Wren6991/RISCBoy/doc/diagrams/ppu_coord_screen.pdf

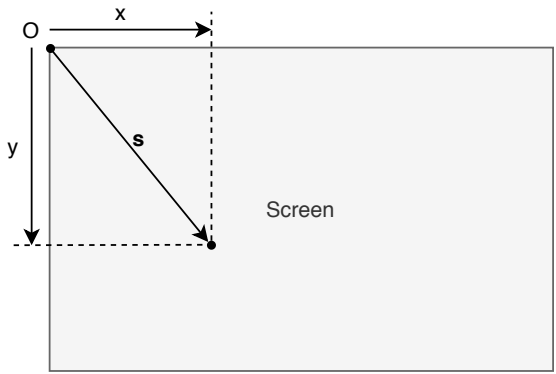
[picture p20: figure]
Screen
