Wren6991/RISCBoy/doc/diagrams/ppu_coord_texture.pdf

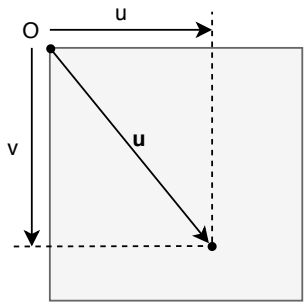
[picture p21: figure]
