Wren6991/RISCBoy/doc/diagrams/ppu_bg_coords.pdf

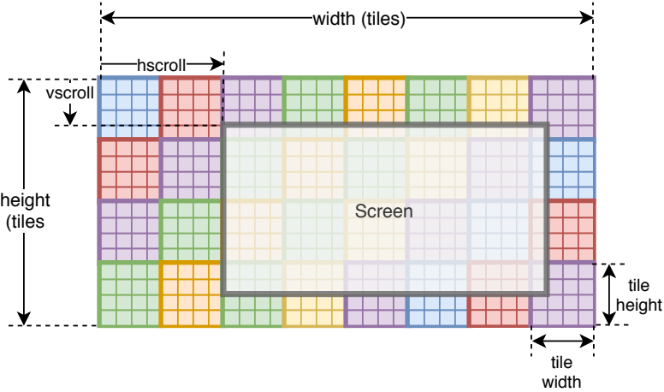
[picture p22: figure]
Screen; hscroll; vscroll; width (tiles); height (tiles; tile height; tile width
