Wren6991/RISCBoy/board/riscboy_reva0/datasheet/SPI LCD from AliExpress.jpg

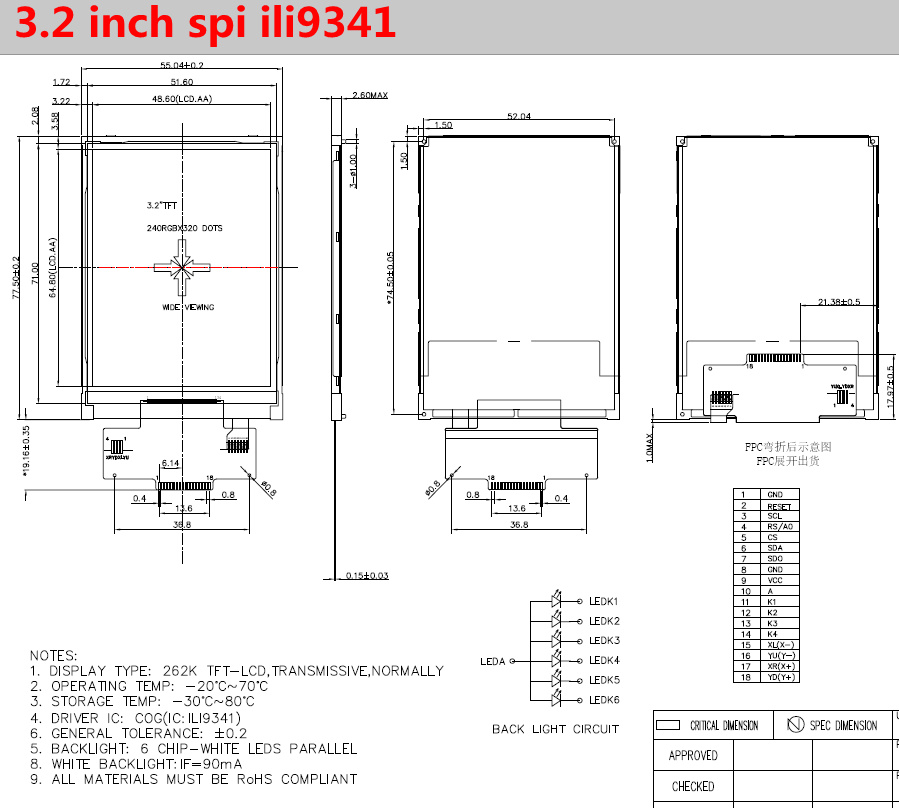
board/riscboy_reva0/datasheet/SPI LCD from AliExpress.jpg
