Wren6991/RISCBoy/software/apps/spin_demo/wilber.png

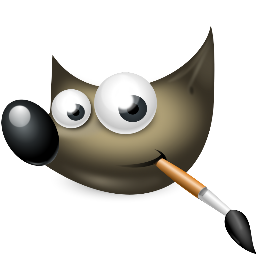
software/apps/spin_demo/wilber.png
