Wren6991/RISCBoy/software/apps/ulx3s_spin/ulx3s.png

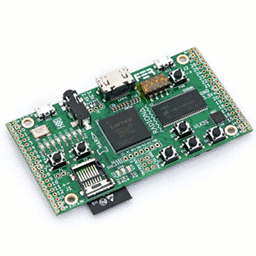
software/apps/ulx3s_spin/ulx3s.png
