Wren6991/RISCBoy/software/graphics/assets/abandonauts/tiles.png

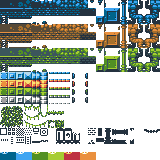
software/graphics/assets/abandonauts/tiles.png
