Wren6991/RISCBoy/software/graphics/assets/arcade_platformer/arcade_platformerV2.png

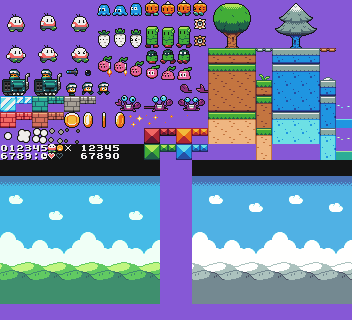
software/graphics/assets/arcade_platformer/arcade_platformerV2.png
