Wren6991/RISCBoy/software/graphics/assets/arcade_platformer/arcade_platformerV2_transparent.png

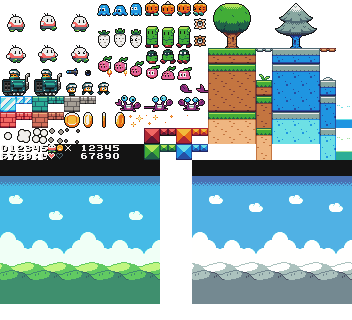
software/graphics/assets/arcade_platformer/arcade_platformerV2_transparent.png
