Wren6991/RISCBoy/software/graphics/assets/colony/colony_0.png

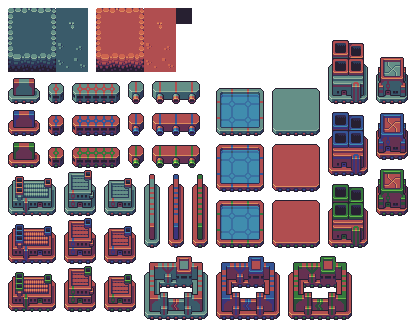
software/graphics/assets/colony/colony_0.png
