Wren6991/RISCBoy/software/graphics/assets/platformer_art_deluxe_pixel_edition/sample.png

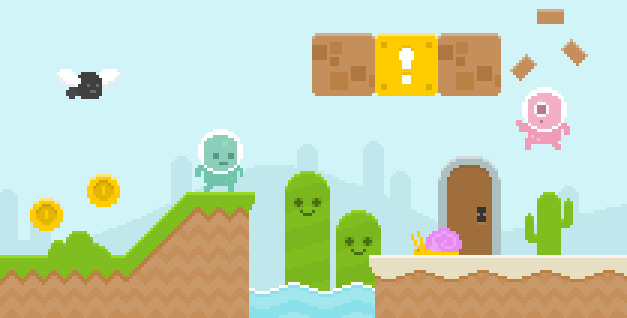
software/graphics/assets/platformer_art_deluxe_pixel_edition/sample.png
