Wren6991/RISCBoy/software/graphics/assets/platformer_art_deluxe_pixel_edition/spritesheet.png

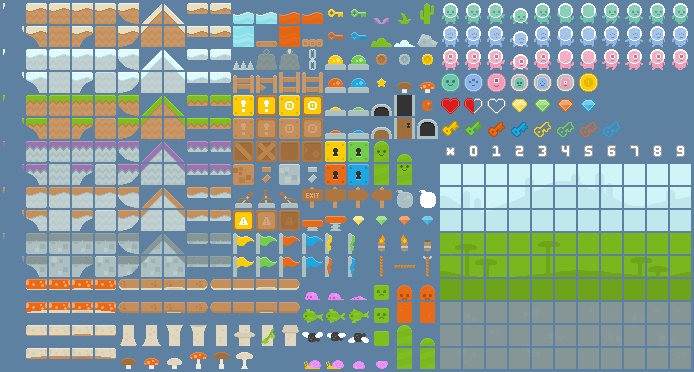
software/graphics/assets/platformer_art_deluxe_pixel_edition/spritesheet.png
