Wren6991/RISCBoy/test/ppu/testcases/blit_smoke_argb1555/expected_output.png

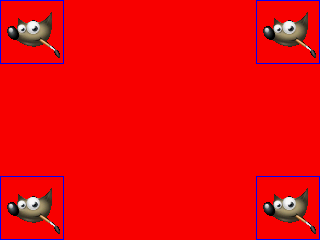
test/ppu/testcases/blit_smoke_argb1555/expected_output.png
