Wren6991/RISCBoy/test/ppu/testcases/tile_clip/expected_output.png

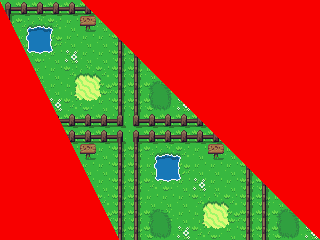
test/ppu/testcases/tile_clip/expected_output.png
