Wren6991/RISCBoy/test/ppu/testcases/tile_t16_pf128_argb1555_scrollneg/expected_output.png

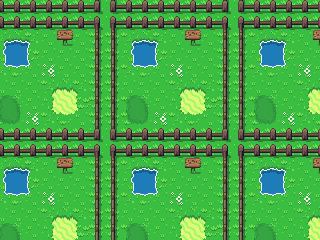
test/ppu/testcases/tile_t16_pf128_argb1555_scrollneg/expected_output.png
