Wren6991/RISCBoy/doc/diagrams/system_arch.pdf

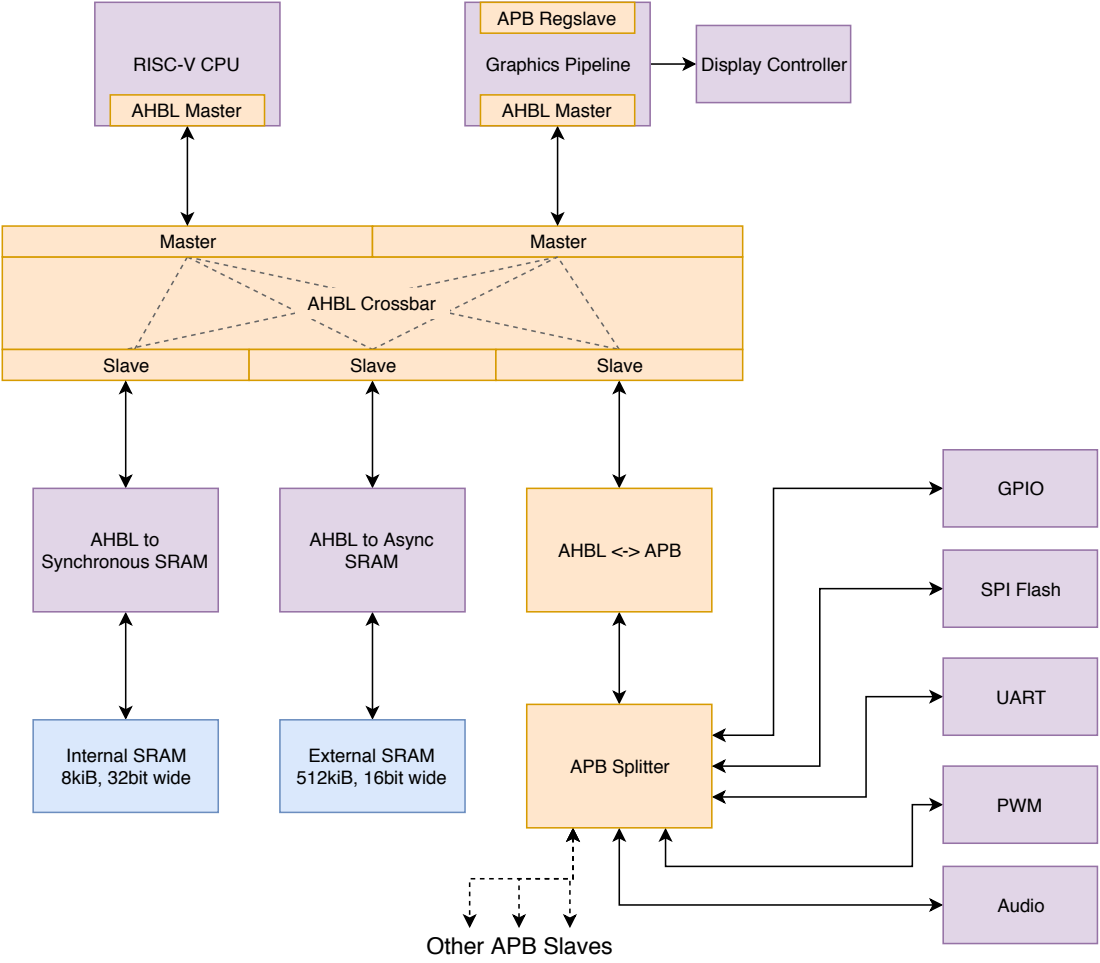
[picture p46: page 1]
Master; Slave; RISC-V CPU; AHBL Master; Graphics Pipeline; APB Regslave; Display Controller; AHBL to Synchronous SRAM; Internal SRAM 8kiB, 32bit wide; External SRAM 512kiB, 16bit wide; AHBL <-> APB; APB Splitter; UART; PWM; Audio; GPIO; AHBL Crossbar; SPI Flash

AHBL to Async
SRAM

Other APB Slaves
