Wren6991/RISCBoy/doc/diagrams/cpu_backend.pdf

Stage D | Clock
Stage M | Clock

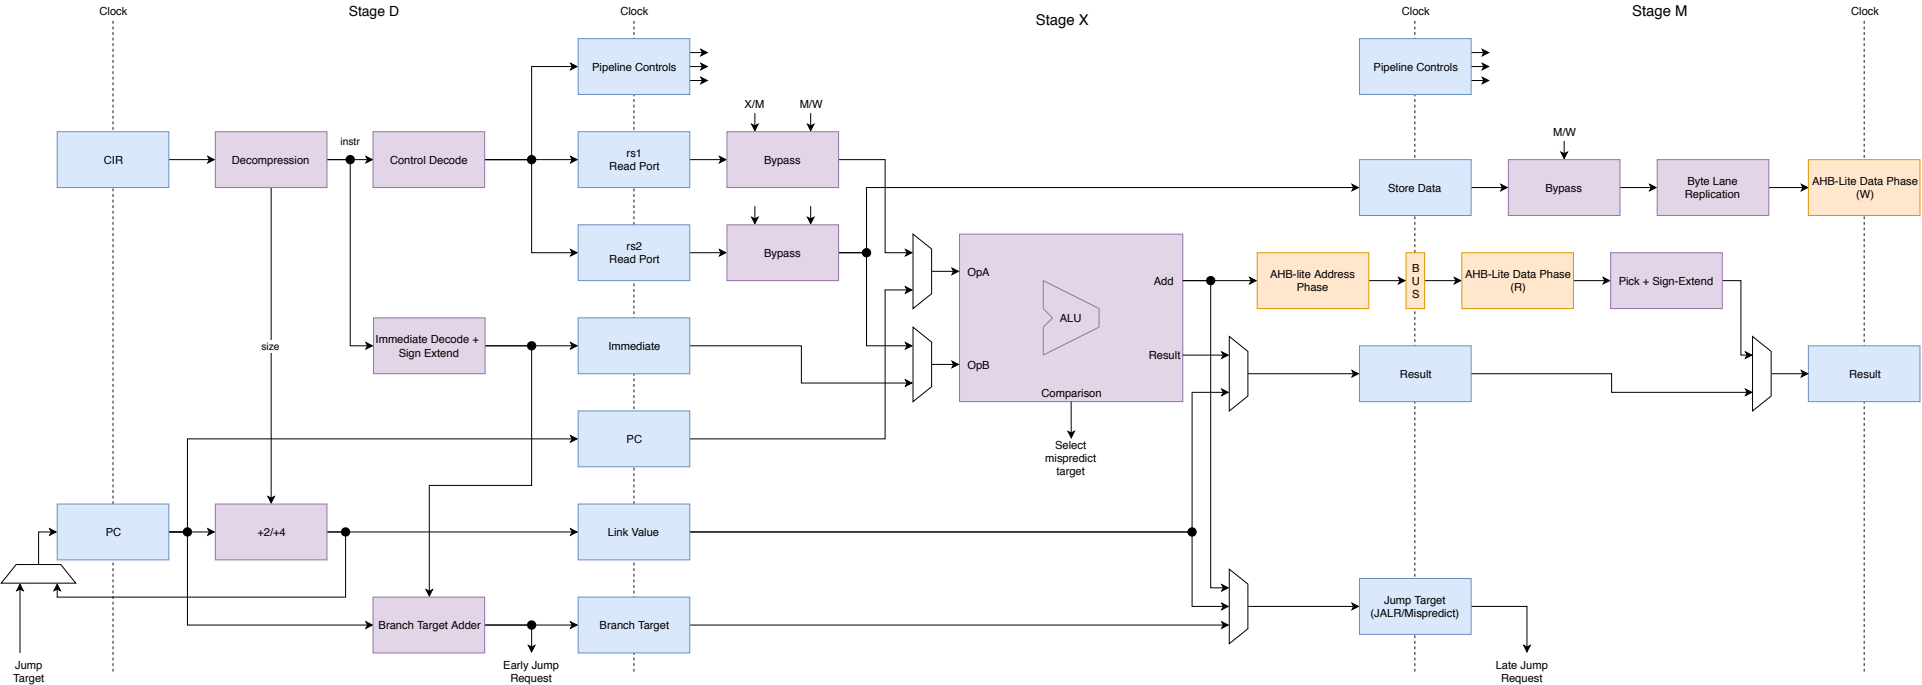
[picture p47: page 1]
rs1 Read Port; rs2 Read Port; CIR; size; instr; Decompression; Branch Target; Link Value; Immediate; Control Decode; Immediate Decode + Sign Extend; Pipeline Controls; Clock; Stage X Clock; ALU; OpA; OpB; Add; Comparison; Result; Bypass; Early Jump Request; Jump Target; Jump Target (JALR/Mispredict); Late Jump Request; Store Data; Byte Lane Replication; Select mispredict target

AHB-Lite Data Phase

AHB-lite Address
Phase

Pick + Sign-Extend

Branch Target Adder
