Wren6991/RISCBoy/board/sram_dev_board/sram_dev_board.pdf

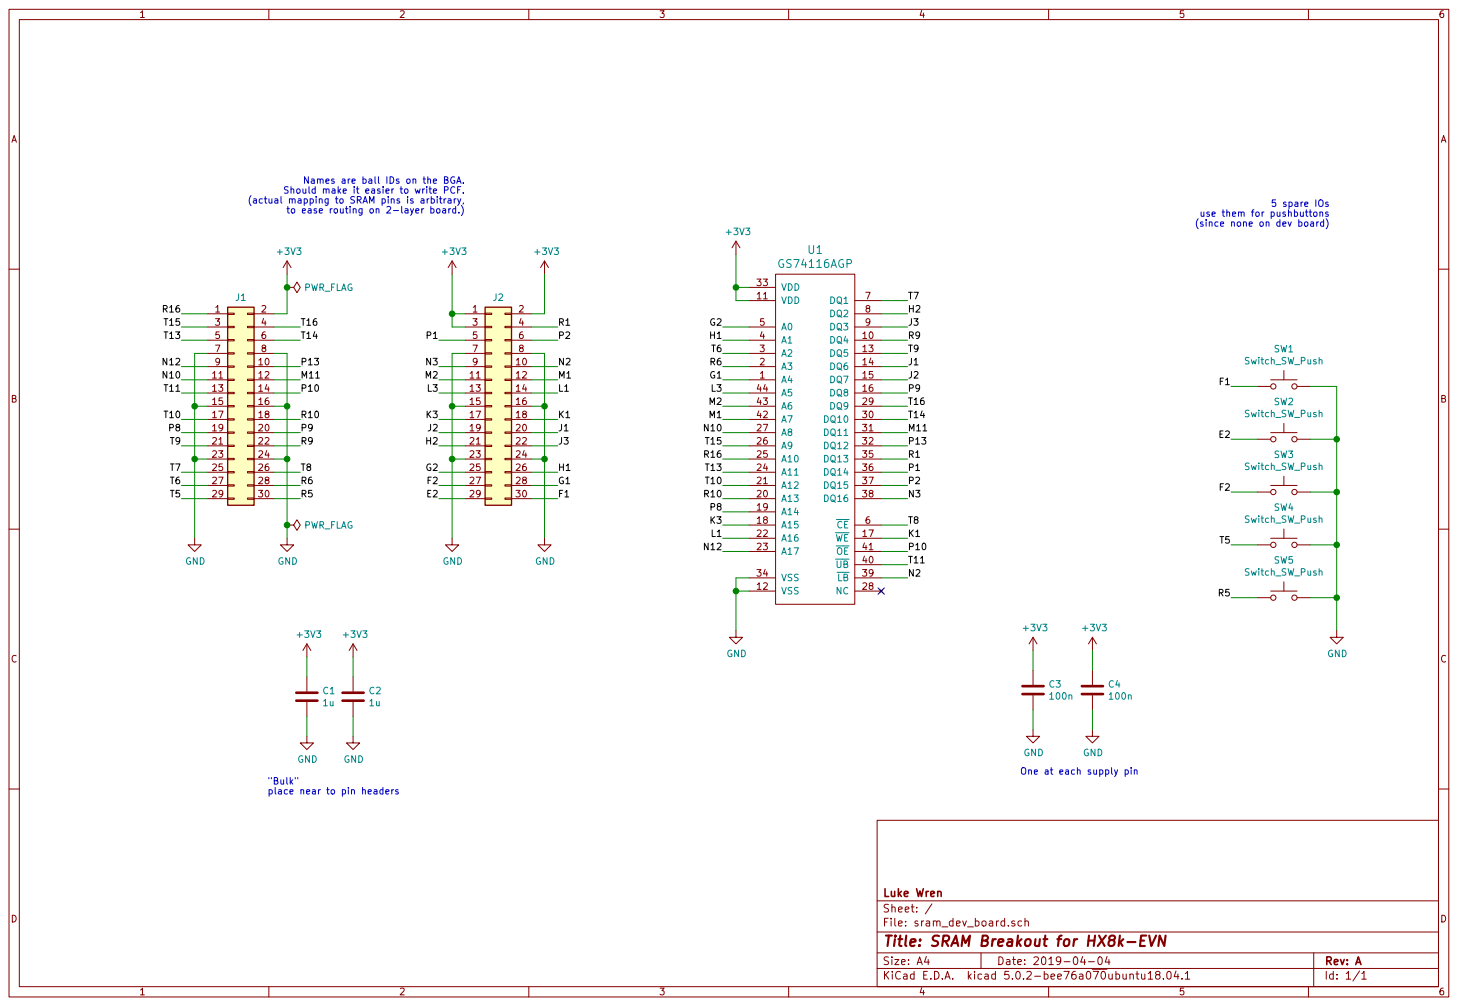
[picture p48: page 1]

(since none on dev board) SW2 Switch_SW_Push SW3 Switch_SW_Push SW4 Switch_SW_Push GND

J2H2 G2F2E2 Names are ball IDs on the BGA. Should make it easier to write PCF. (actual mapping to SRAM pins is arbitrary,

use them for pushbuttons

+3V3 One at each supply pin

"Bulk" place near to pin headers

File: sram_dev_board.sch Sheet: / Luke Wren

Id: 1/1 Title: SRAM Breakout for HX8k-EVN
