Wren6991/RISCBoy/doc/diagrams/cpu_frontend.pdf

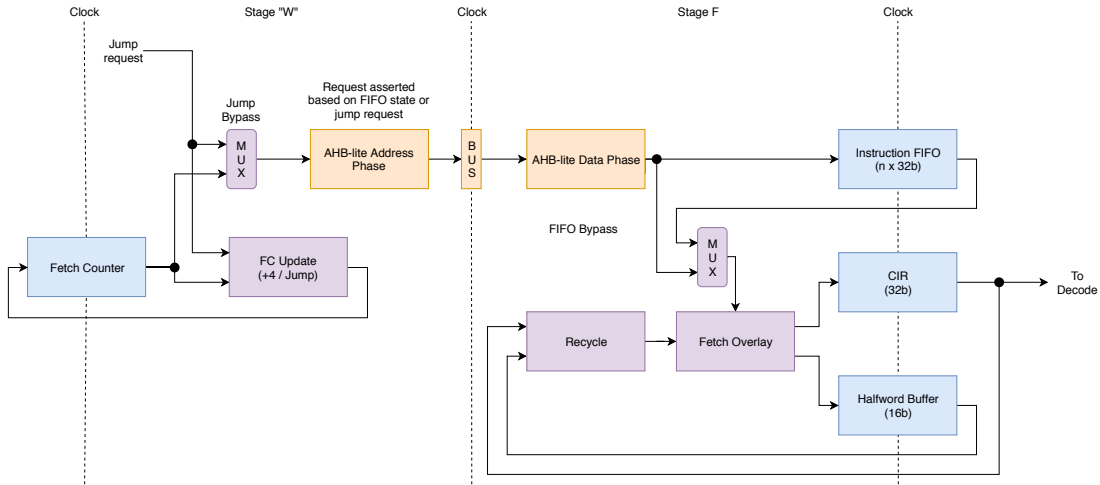
[picture p49: page 1]
Instruction FIFO (n x 32b); Halfword Buffer (16b); CIR (32b); To Decode; Clock; Recycle; Fetch Overlay; FIFO Bypass; Fetch Counter; FC Update (+4 / Jump); Jump request; Stage "W"; Stage F; Jump Bypass

Request asserted
based on FIFO state or
jump request

AHB-lite Address
Phase

AHB-lite Data Phase
