Wren6991/RISCBoy/board/riscboy_reva0/fpgaboy.pdf

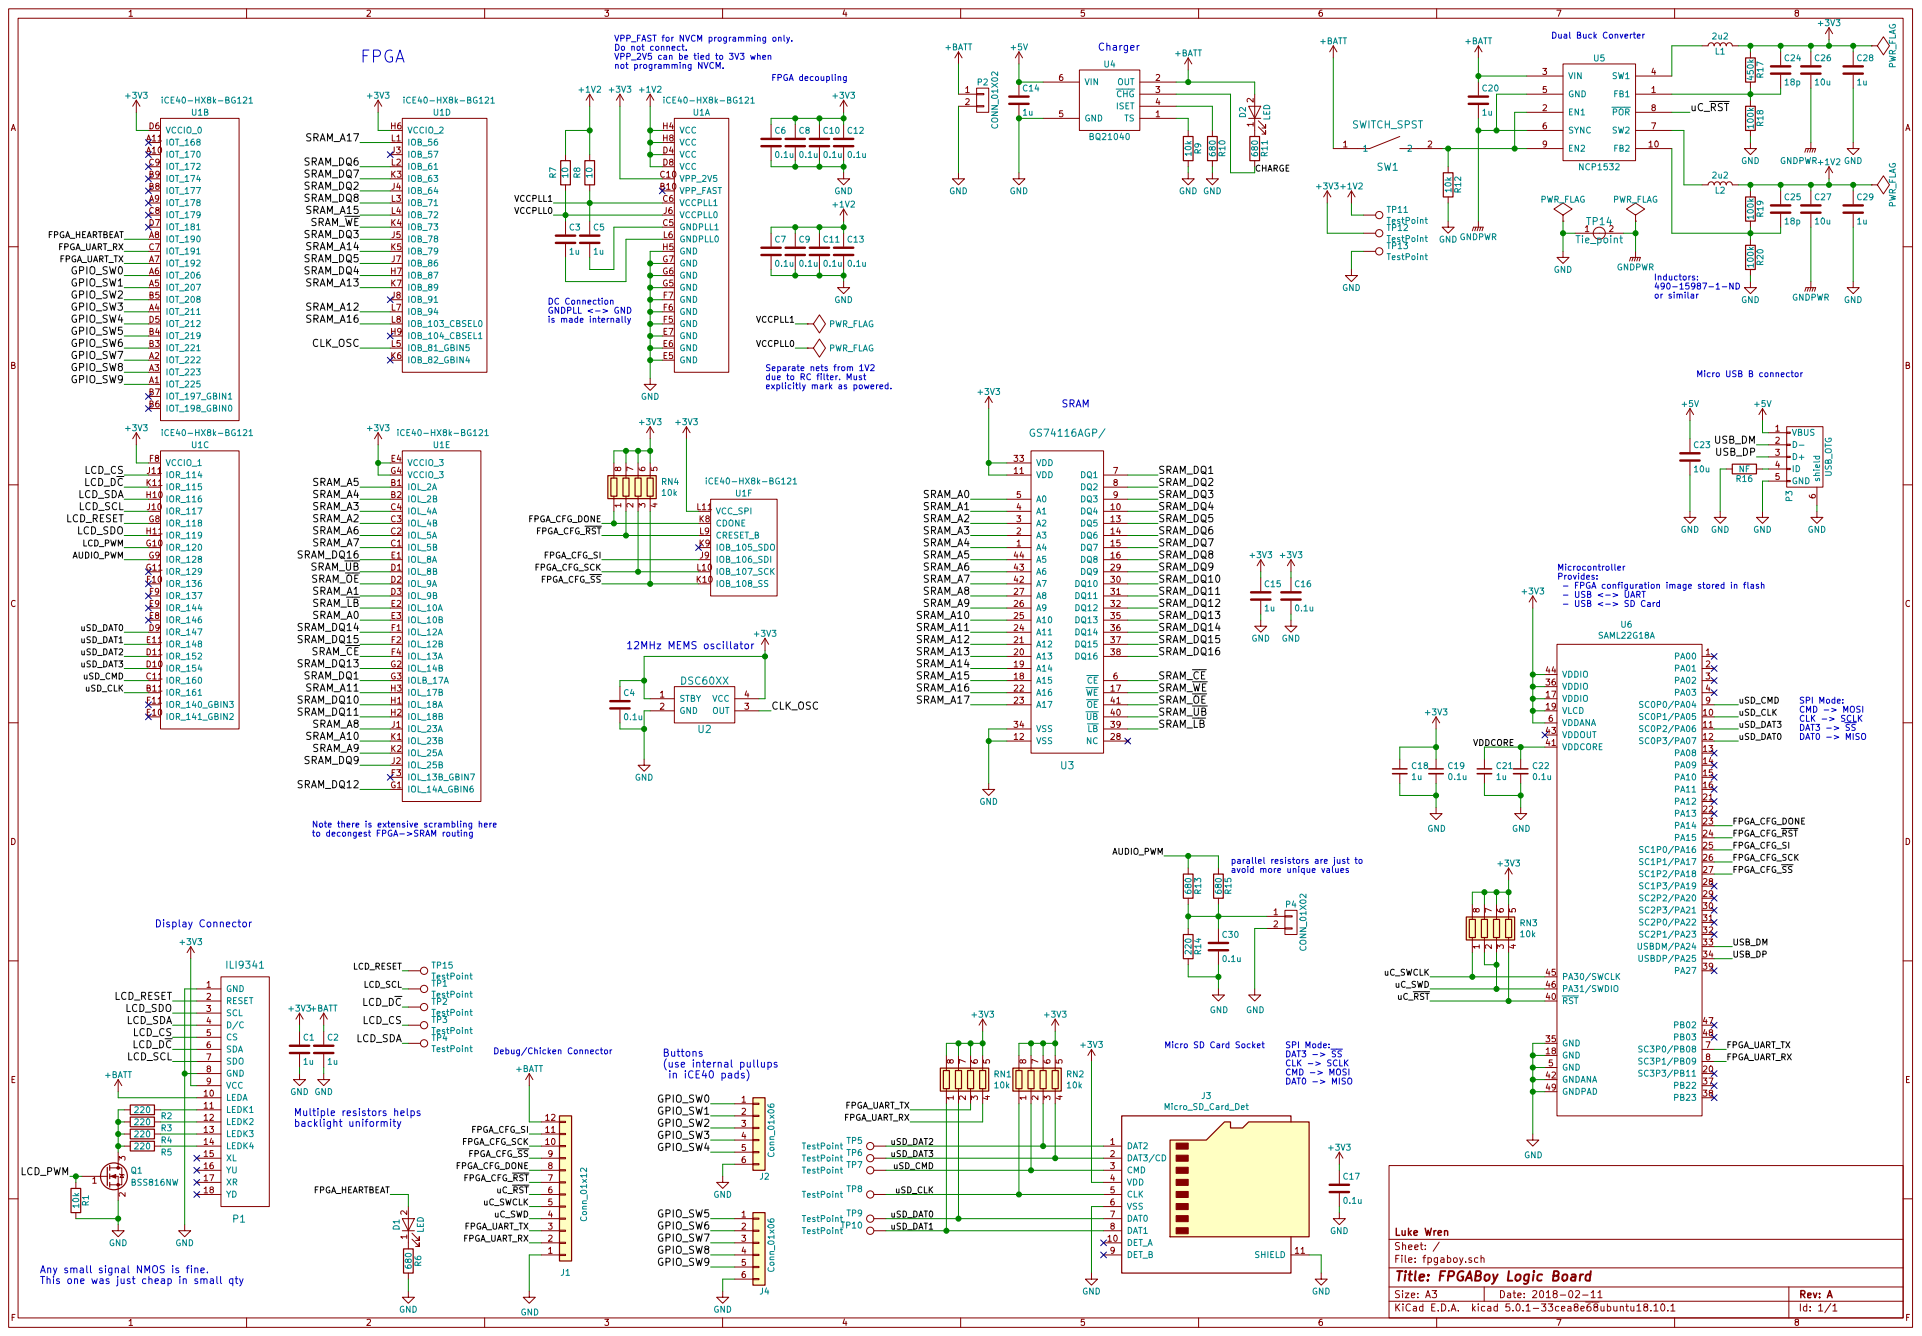
[picture p50: page 1]

VPP_FAST for NVCM programming only. Do not connect. VPP_2V5 can be tied to 3V3 when
not programming NVCM. +3V3

DC Connection GNDPLL <-> GND

Separate nets from 1V2
due to RC filter. Must explicitly mark as powered.

Note there is extensive scrambling here
to decongest FPGA->SRAM routing

parallel resistors are just to
avoid more unique values

SPI Mode: DAT3 -> SS CLK -> SCLK CMD -> MOSI DAT0 -> MISO

File: fpgaboy.sch Sheet: / Luke Wren

This one was just cheap in small qty GND

Any small signal NMOS is fine.

Id: 1/1 Title: FPGABoy Logic Board
