Wren6991/RISCBoy/doc/diagrams/stackup_and_bga.pdf

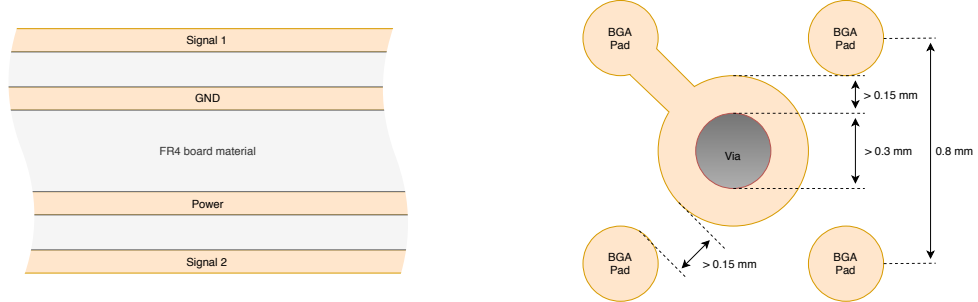
[picture p51: page 1]
BGA Pad; Via; Signal 1; GND; Power; Signal 2; FR4 board material
