Wren6991/RISCBoy/doc/waves/sync_sram_ahb_stall.pdf

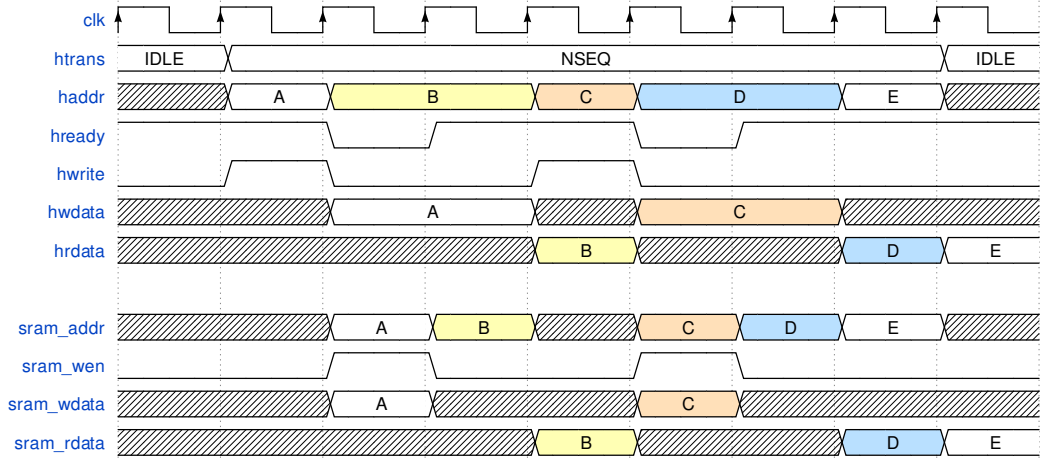
[picture p61: page 1]
clk; htrans; IDLE; NSEQ; haddr; hready; hwrite; hwdata; hrdata; sram_addr; sram_wen; sram_wdata; sram_rdata
