Wren6991/RISCBoy/doc/waves/sync_sram_only.pdf

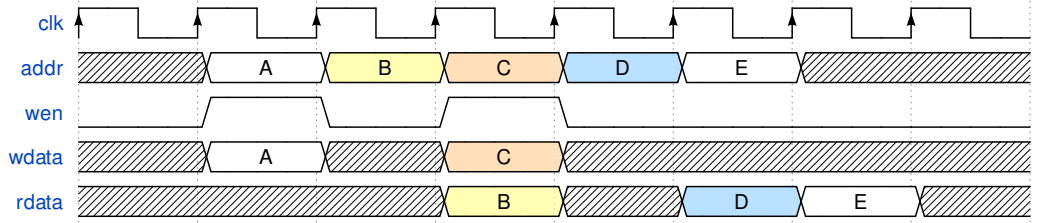
[picture p62: page 1]
clk; addr; wen; wdata; rdata
