Wren6991/RISCBoy/doc/diagrams/ppu_buffer_states.pdf

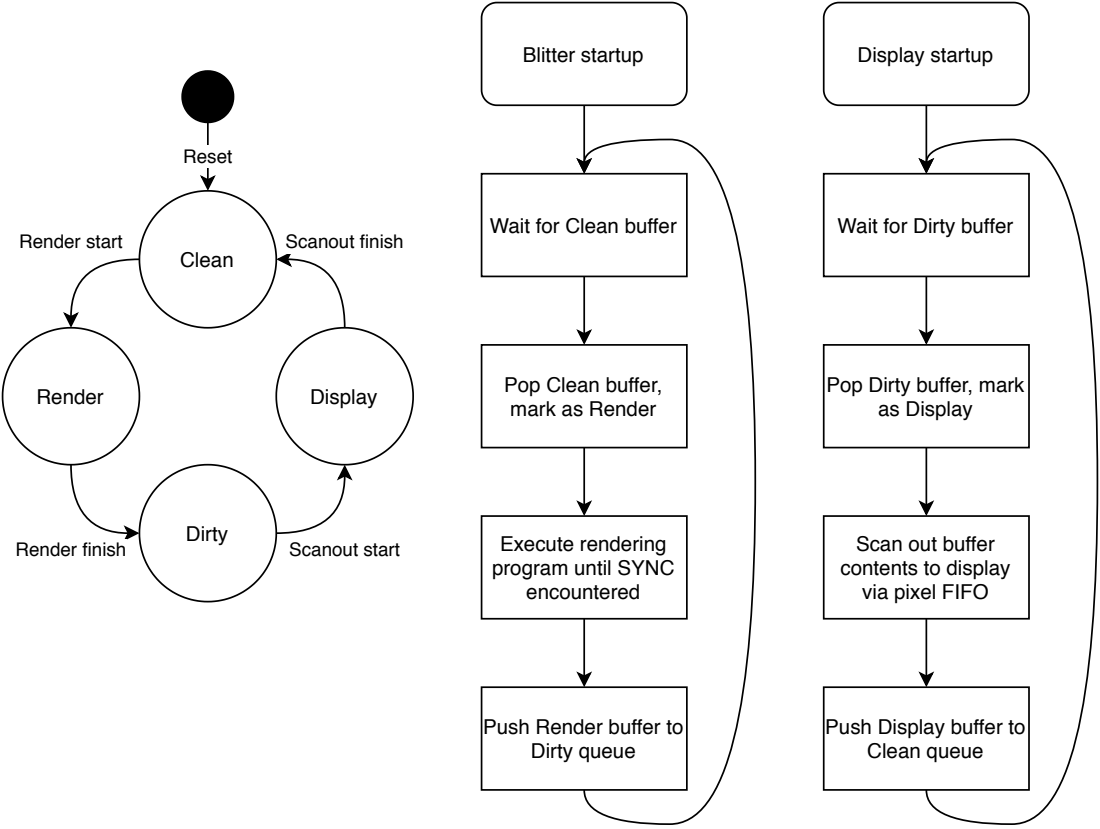
[picture p63: page 1]
Render finish; Render; Scanout start; Dirty; Scanout finish; Display; Render start; Clean; Blitter startup; Display startup; Reset

Wait for Clean buffer

Wait for Dirty buffer

Pop Clean buffer,
mark as Render

Pop Dirty buffer, mark
as Display

Execute rendering
program until SYNC
encountered

Scan out buffer
contents to display
via pixel FIFO

Push Render buffer to
Dirty queue

Push Display buffer to
Clean queue
