Wren6991/RISCBoy/doc/diagrams/ppu_texture_ablit04.pdf

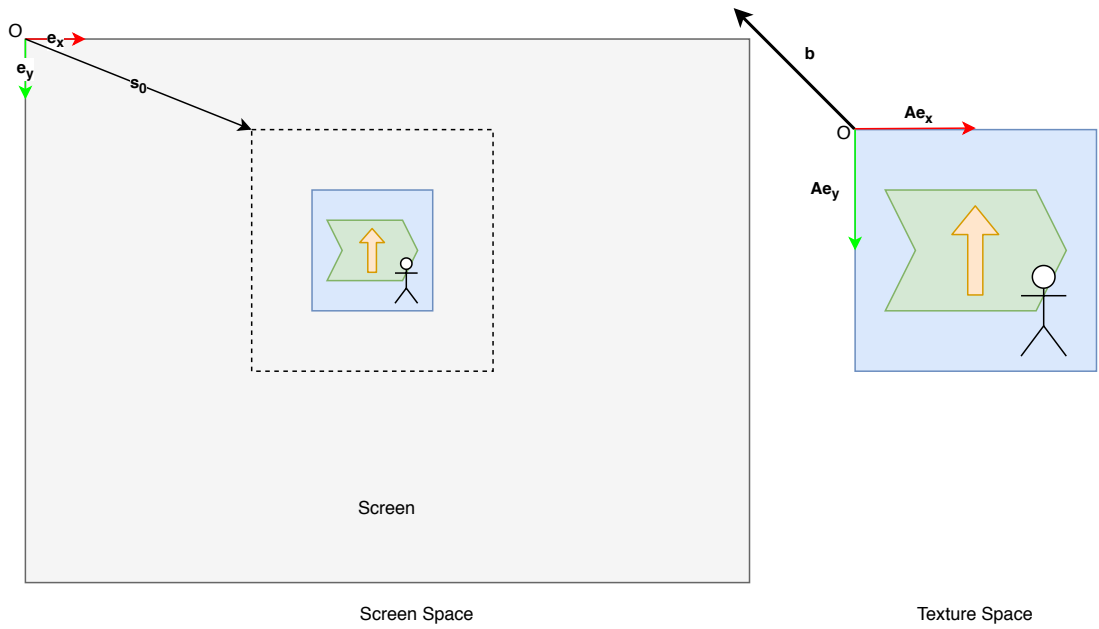
[picture p64: page 1]
Screen; Aex; Aey; Screen Space; Texture Space
