Wren6991/RISCBoy/doc/diagrams/ppu_texture_ablit05.pdf

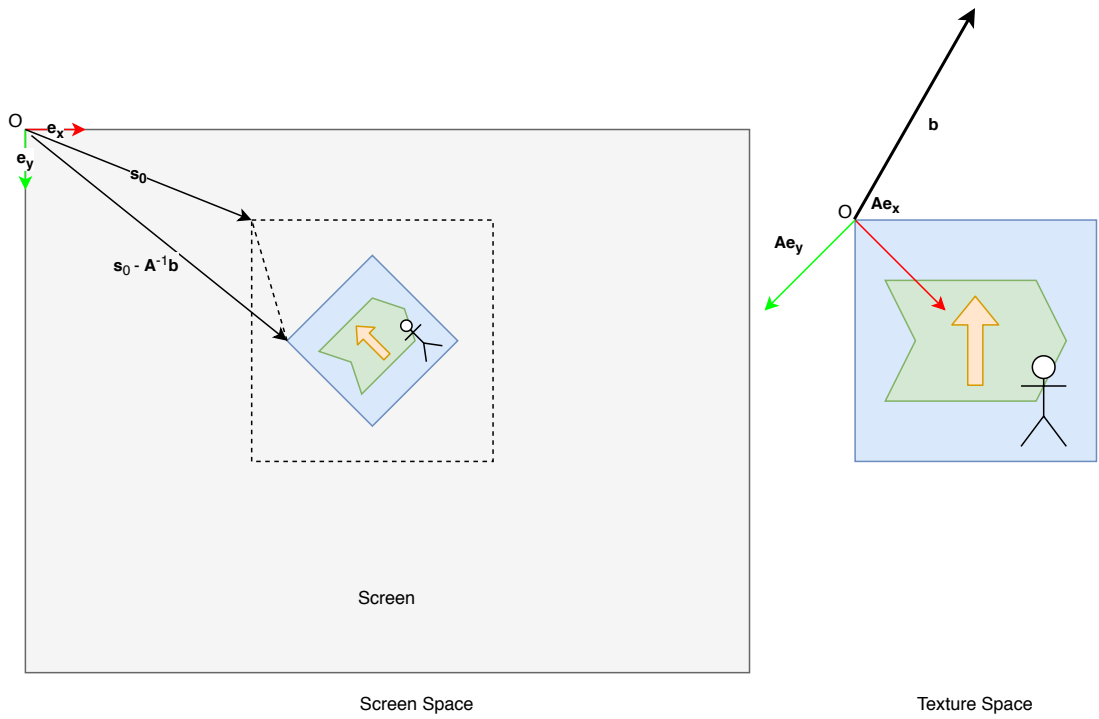
[picture p65: page 1]
Screen; Aex; Aey; Screen Space; Texture Space
