Wren6991/RISCBoy/doc/diagrams/ppu_texture_ablit01.pdf

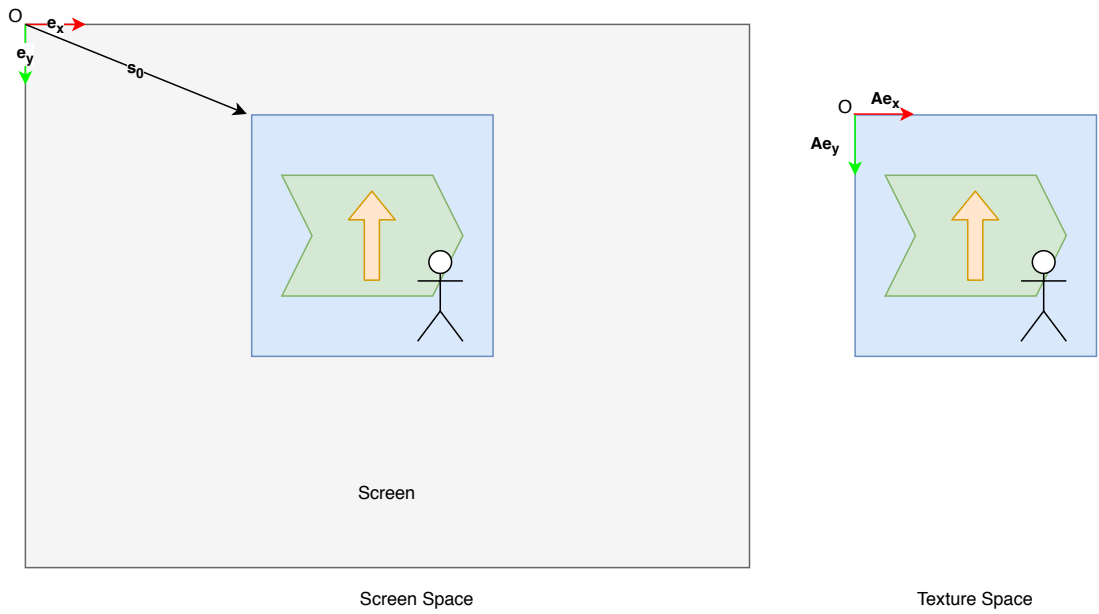
[picture p66: page 1]
Screen; Aex; Aey; Screen Space; Texture Space
