Wren6991/RISCBoy/doc/diagrams/ppu_texture_ablit02.pdf

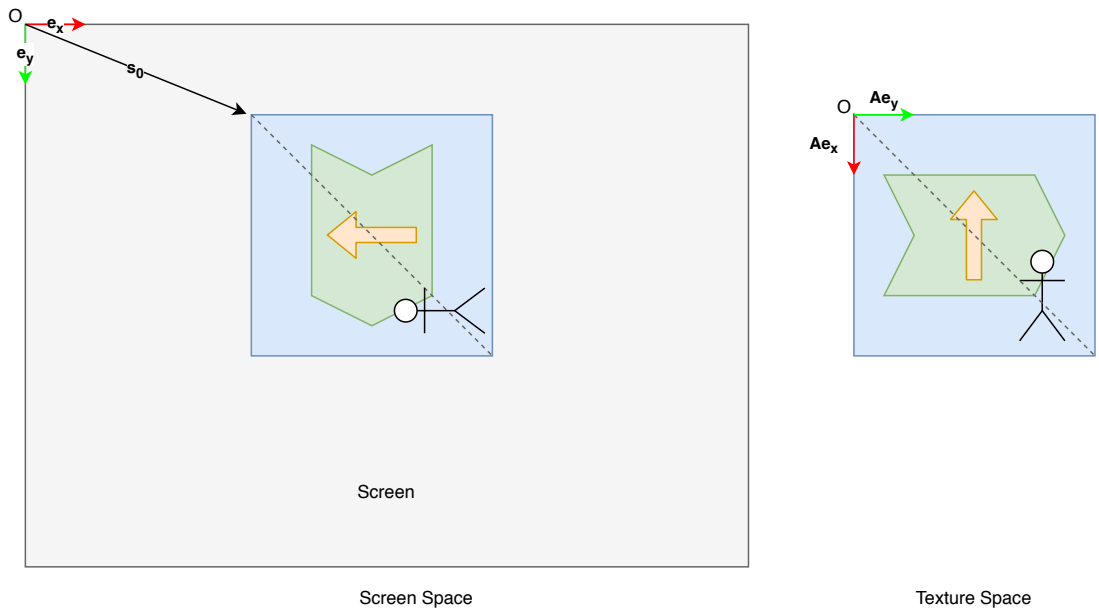
[picture p67: page 1]
Screen; Aex; Aey; Screen Space; Texture Space
