Wren6991/RISCBoy/doc/diagrams/ppu_texture_ablit03.pdf

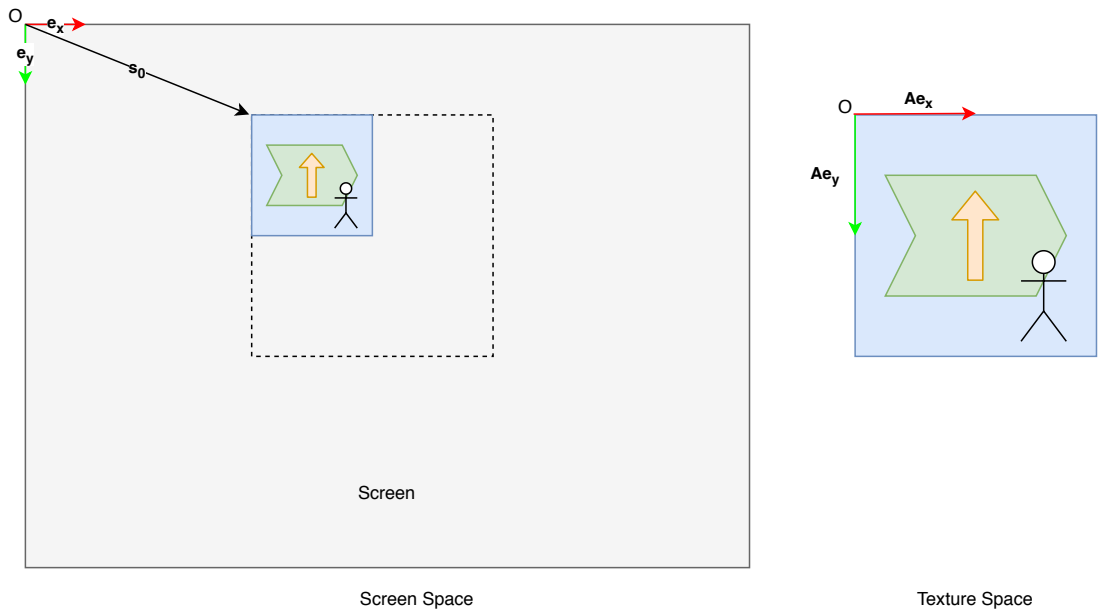
[picture p68: page 1]
Screen; Aex; Aey; Screen Space; Texture Space
