Wren6991/RISCBoy/doc/diagrams/ppu_texture_example.pdf

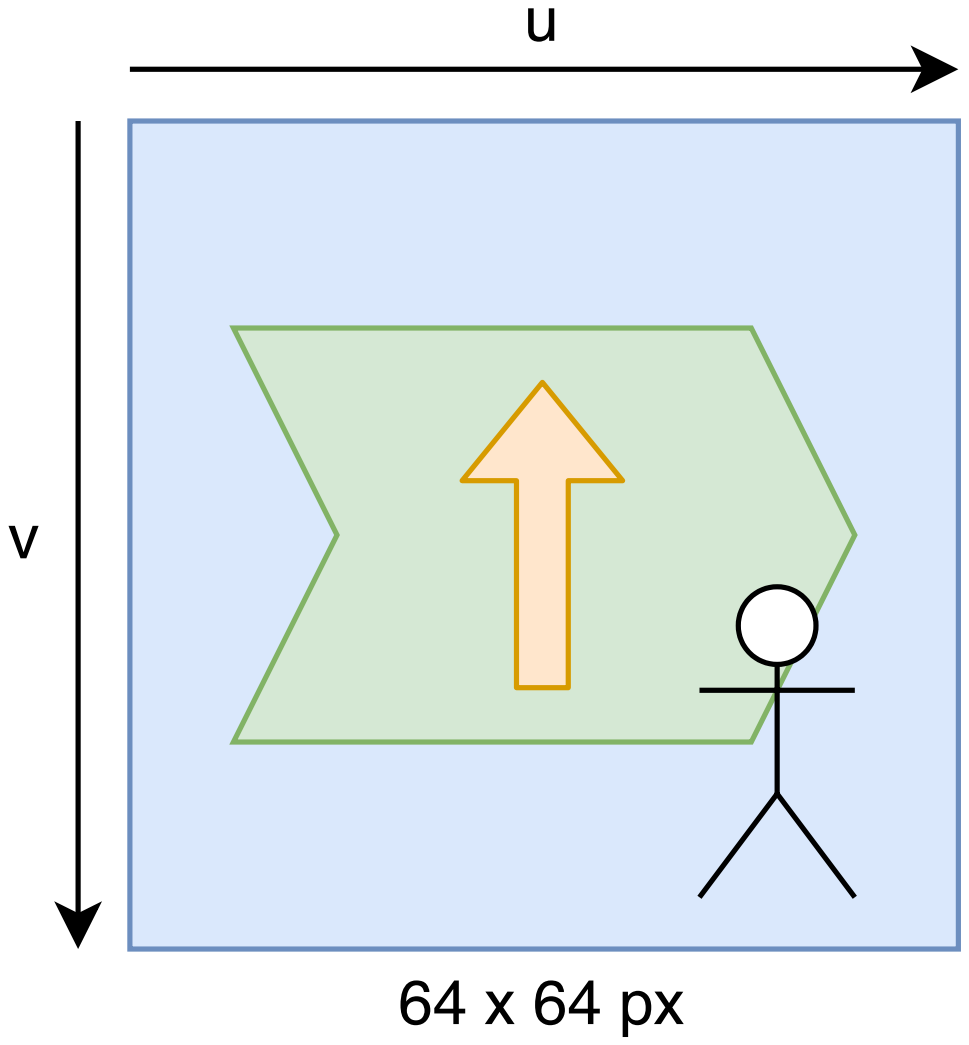
[picture p69: page 1]
