Wren6991/RISCBoy/doc/diagrams/unaligned_accesses.pdf

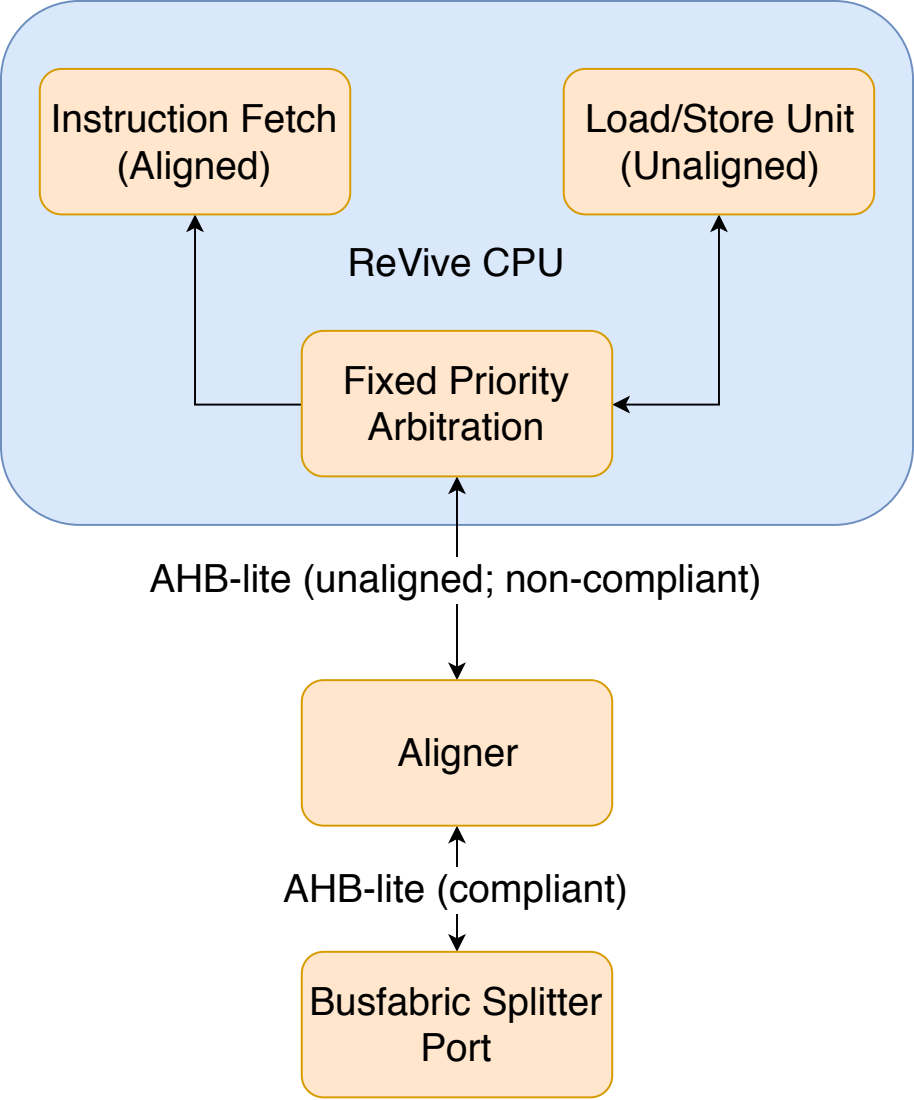
[picture p70: page 1]
ReVive CPU; Instruction Fetch (Aligned); Fixed Priority Arbitration; Aligner; Busfabric Splitter Port

Load/Store Unit
(Unaligned)

AHB-lite (unaligned; non-compliant)

AHB-lite (compliant)
