Wren6991/RISCBoy/doc/diagrams/crossbar_structure.pdf

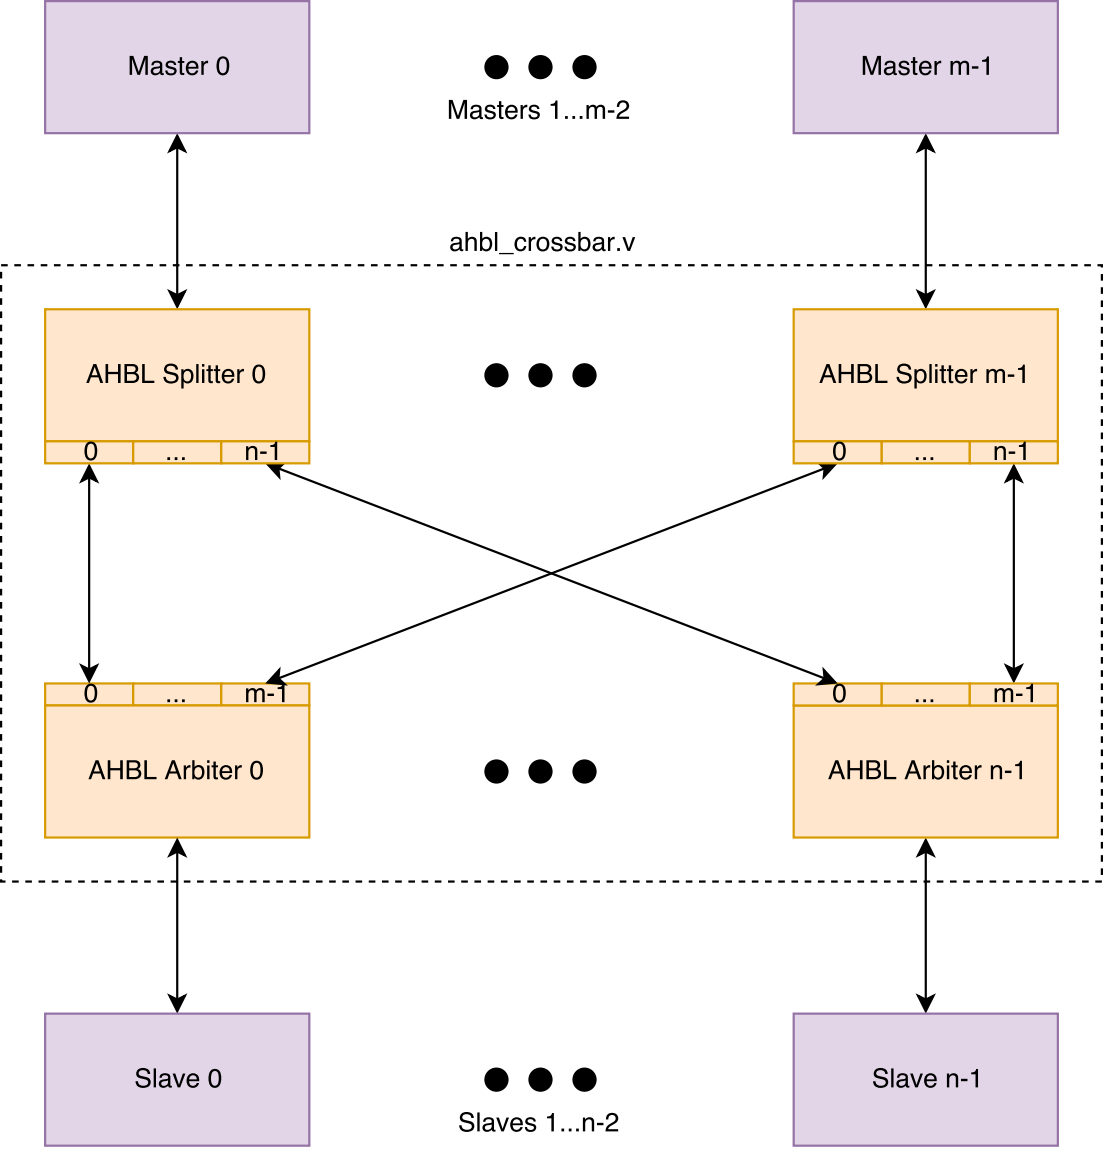
[picture p71: page 1]
